acornelissen/IDENTIDEM.design-LRF45/3MF/lrf45-ground-glass-guide.3mf

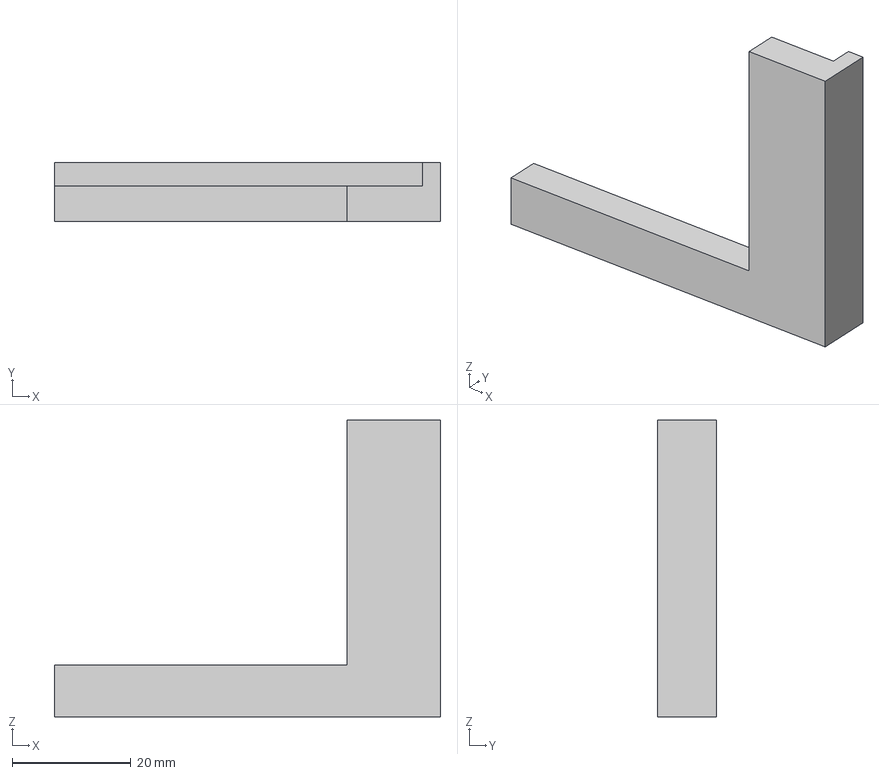
[picture p15: CAD file, 2024-04-28]
3MF/lrf45-ground-glass-guide.3mf
65.0 x 10.0 x 50.0 mm
